tomaszbk/escape_room/src/uno/led.cpp

#include <Arduino.h>
#include "Led.h"

void setupLed()
{
    pinMode(LED1, OUTPUT);
    pinMode(LED2, OUTPUT);
    pinMode(WRONG_LED, OUTPUT);
}

void ledOneOn(){
    digitalWrite(LED1, HIGH);
}

void ledTwoOn(){
    digitalWrite(LED2, HIGH);
}

void ledWrongBlink(){
    digitalWrite(WRONG_LED, HIGH);
    delay(250);
    digitalWrite(WRONG_LED, LOW);
    delay(250);
    digitalWrite(WRONG_LED, HIGH);
    delay(250);
    digitalWrite(WRONG_LED, LOW);
}
void ledWrongOn(){
    digitalWrite(WRONG_LED, HIGH);
}
void ledWrongOff(){
    digitalWrite(WRONG_LED, LOW);
}
void ledsOff(){
    digitalWrite(LED1, LOW);
    digitalWrite(LED2, LOW);
    digitalWrite(WRONG_LED, LOW);
}
